mlab-modules/RETERMINT01/doc/gen/dxf/RETERMINT01-B_Cu.dxf

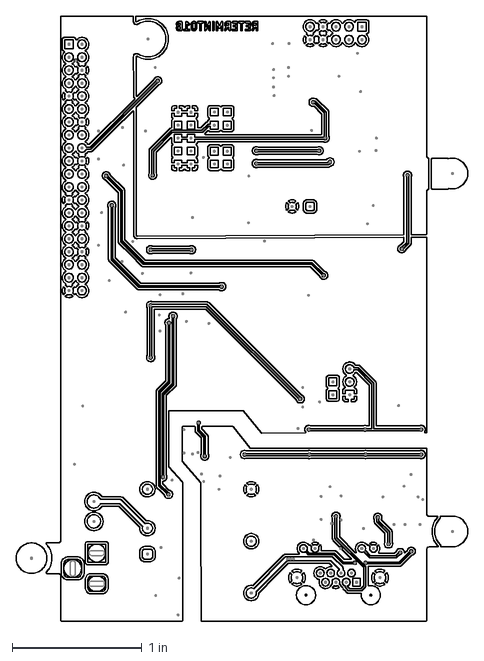
[picture p12: CAD file, 2026-08-13]
doc/gen/dxf/RETERMINT01-B_Cu.dxf
3.48 x 4.67 in
